anfractuosity/wavecatcher/software/process.c

#include <stdio.h>

// from http://cs-fundamentals.com/tech-interview/c/c-program-to-count-number-of-ones-in-unsigned-integer.php
int countSetBits(unsigned int n) {
    n = n - ((n >> 1) & 0x55555555);
    n = (n & 0x33333333) + ((n >> 2) & 0x33333333);
    n = (n + (n >> 4)) & 0x0F0F0F0F;
    n = n + (n >> 8);
    n = n + (n >> 16);
    return n & 0x0000003F;
}

// This should be replaced with moving average filter
//
// play output using something like:
//
// sox -r 20000 -c 1 -b 8 -t raw -e unsigned-integer out.bin 1.wav
int process() {

    int i = 0;

    FILE *o = fopen("out.bin", "ab");
    FILE *f = fopen("dump.bin", "rb");

    char buf[32];

    while ((i = fread(buf, 32, 1, f)) == 1) {
    
        int c = 0;
        int max = 32 / 4;
        int sum = 0;
        for (c = 0; c < max; c++) {
            int val = ((int *)buf)[c];
            sum += countSetBits(val);
        }

        unsigned char tmp = sum;
        fwrite(&tmp, 1, 1, o);
    }

}

int main(){
    process();
}
